William-Dorsch/3d-Printed-AAR-Control-Stand/AARcontroller(v6) - Release/air brake valves/automatic/auto Notch.stl

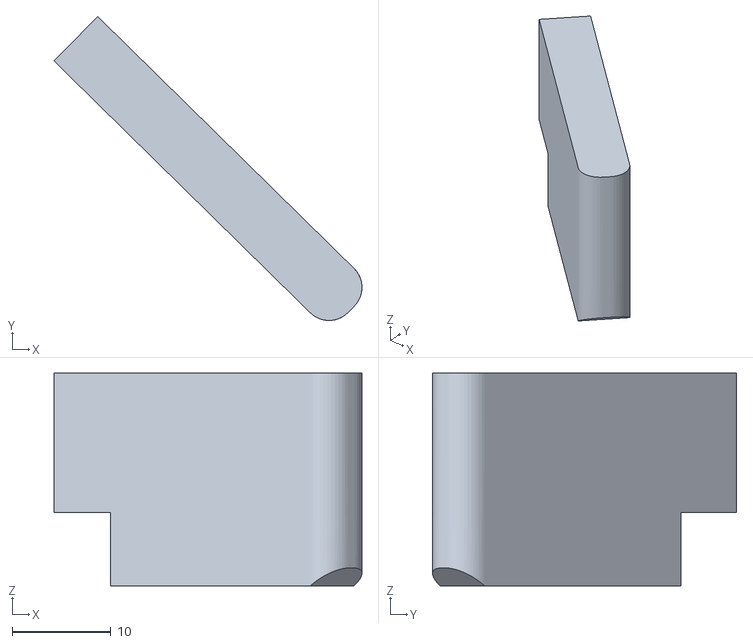
[picture p15: CAD file, 2026-03-23]
AARcontroller(v6) - Release/air brake valves/automatic/auto Notch.stl
31.1 x 30.7 x 21.5
