William-Dorsch/3d-Printed-AAR-Control-Stand/AARcontroller(v6) - Release/air brake valves/independent/indy housing.stl

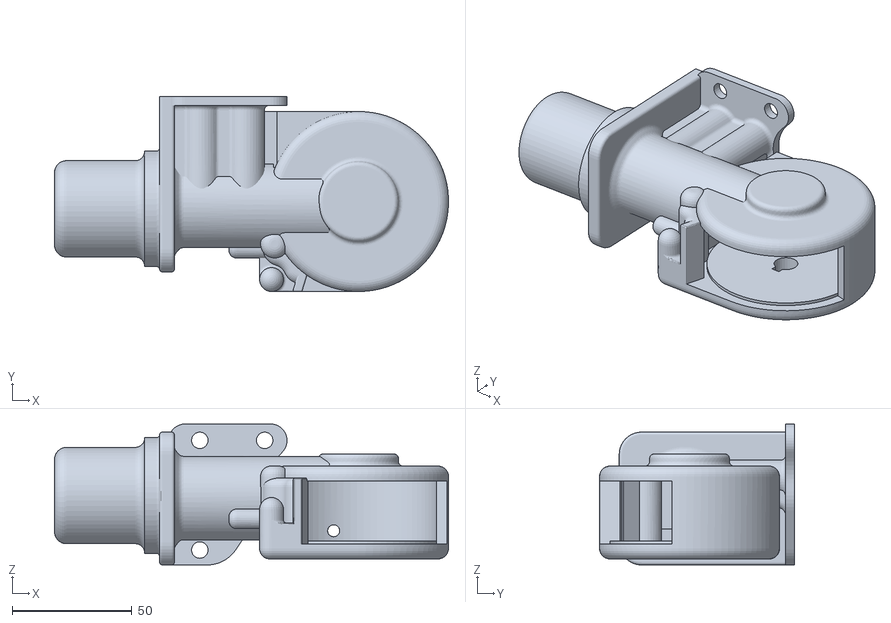
[picture p16: CAD file, 2025-12-22]
AARcontroller(v6) - Release/air brake valves/independent/indy housing.stl
164.2 x 81.3 x 58.8
