William-Dorsch/3d-Printed-AAR-Control-Stand/AARcontroller(v6) - Release/buttons and dials/breakers/linearSwitchBack.3mf

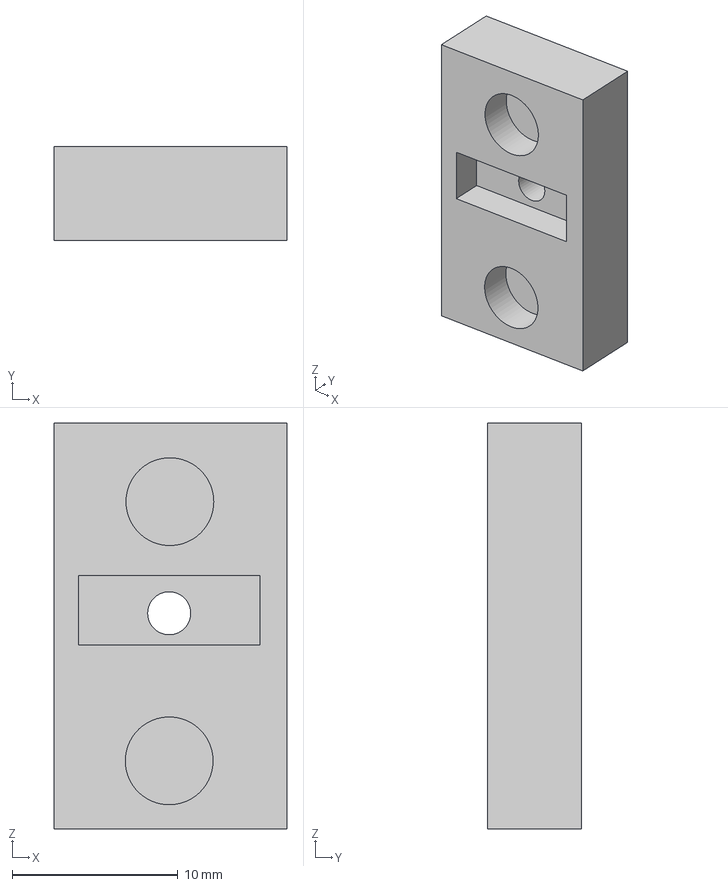
[picture p17: CAD file, 2025-12-27]
AARcontroller(v6) - Release/buttons and dials/breakers/linearSwitchBack.3mf
14.0 x 5.70 x 24.5 mm
