William-Dorsch/3d-Printed-AAR-Control-Stand/AARcontroller(v6) - Release/buttons and dials/horn/horn lever.3mf

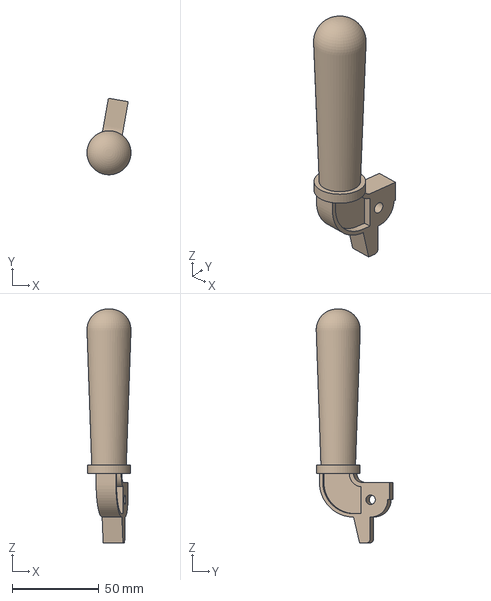
[picture p18: CAD file, 2026-02-25]
AARcontroller(v6) - Release/buttons and dials/horn/horn lever.3mf
25.4 x 44.2 x 135.0 mm
