William-Dorsch/3d-Printed-AAR-Control-Stand/AARcontroller(v6) - Release/buttons and dials/indicator light panel/indicatorLightHousing.stl

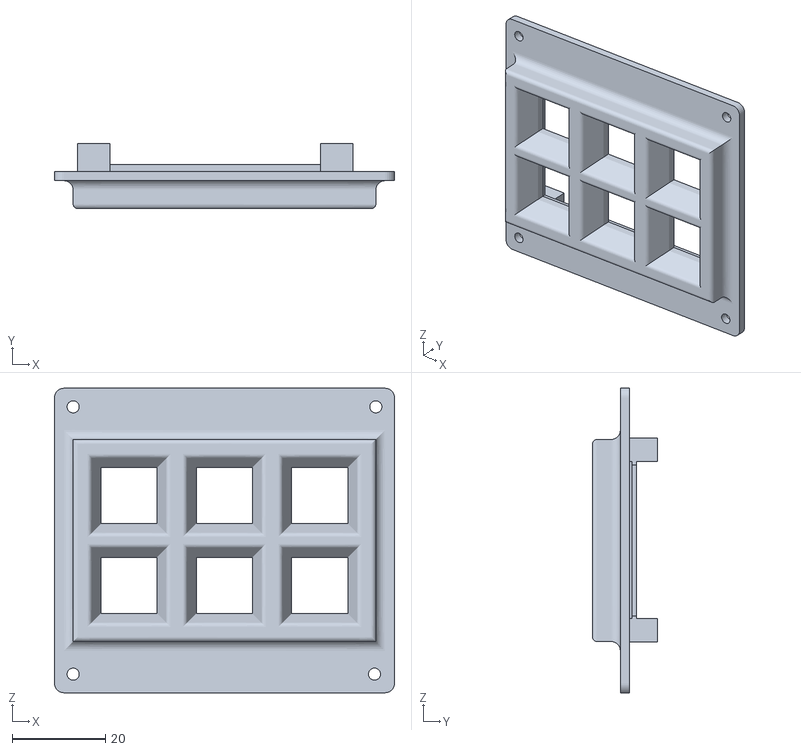
[picture p19: CAD file, 2025-12-22]
AARcontroller(v6) - Release/buttons and dials/indicator light panel/indicatorLightHousing.stl
72.9 x 14.0 x 65.3
