William-Dorsch/3d-Printed-AAR-Control-Stand/AARcontroller(v6) - Release/buttons and dials/light dials v2/rear light dial faceplate.3mf

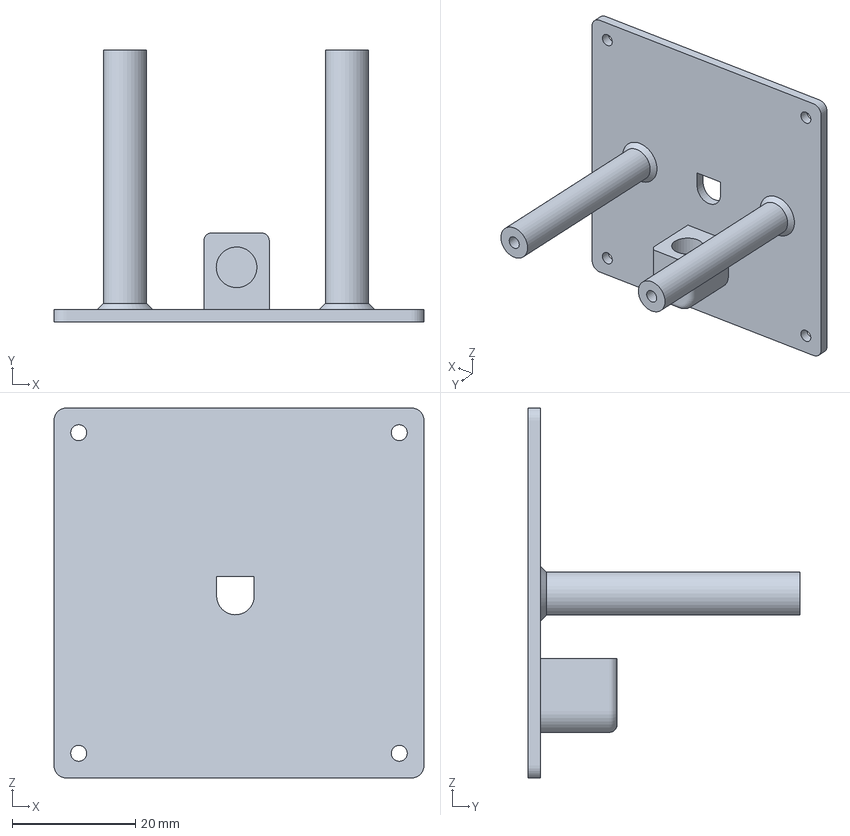
[picture p20: CAD file, 2026-03-18]
AARcontroller(v6) - Release/buttons and dials/light dials v2/rear light dial faceplate.3mf
60.0 x 44.1 x 60.0 mm
