William-Dorsch/3d-Printed-AAR-Control-Stand/AARcontroller(v6) - Release/cutout templates/light dial cutout.stl

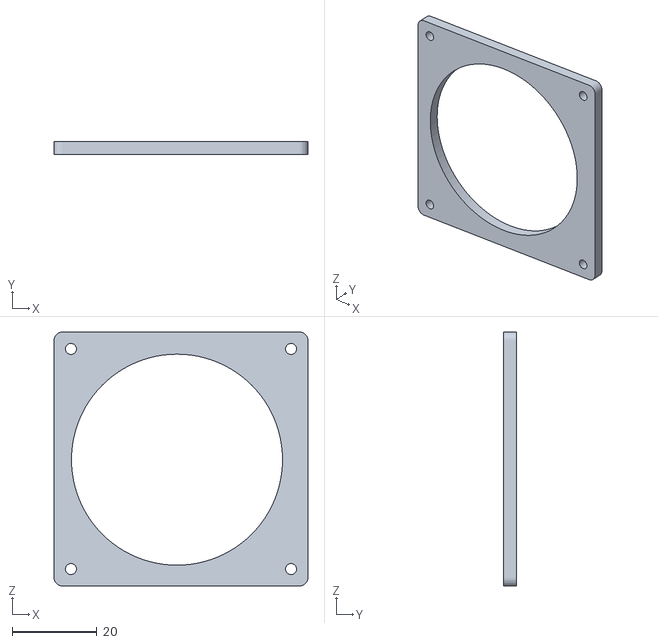
[picture p21: CAD file, 2025-12-22]
AARcontroller(v6) - Release/cutout templates/light dial cutout.stl
60.0 x 3.00 x 60.0
