William-Dorsch/3d-Printed-AAR-Control-Stand/AARcontroller(v6) - Release/throttle and dynamic brake/dynamic brake/dynamic brake label.stl

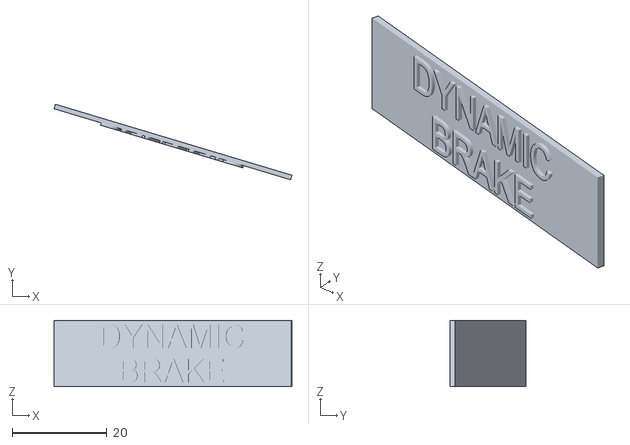
[picture p23: CAD file, 2025-12-22]
AARcontroller(v6) - Release/throttle and dynamic brake/dynamic brake/dynamic brake label.stl
50.3 x 16.0 x 14.0
