William-Dorsch/3d-Printed-AAR-Control-Stand/AARcontroller(v6) - Release/throttle and dynamic brake/throttle and db axle.stl

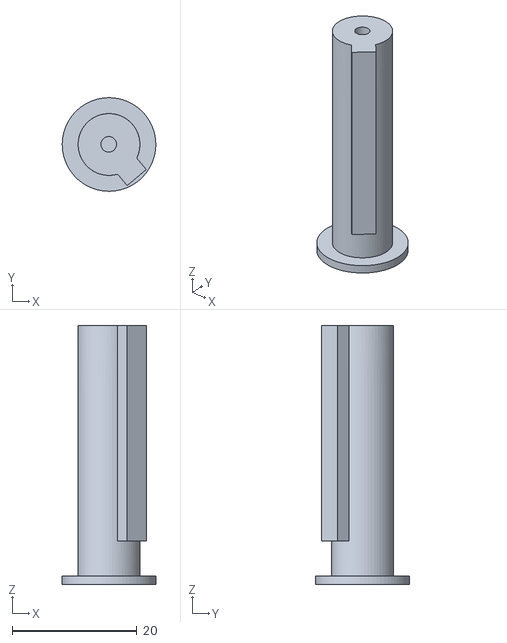
[picture p25: CAD file, 2025-12-22]
AARcontroller(v6) - Release/throttle and dynamic brake/throttle and db axle.stl
15.0 x 15.0 x 41.5
