William-Dorsch/3d-Printed-AAR-Control-Stand/AARcontroller(v6) - Release/throttle and dynamic brake/throttle/throttle notch v2.stl

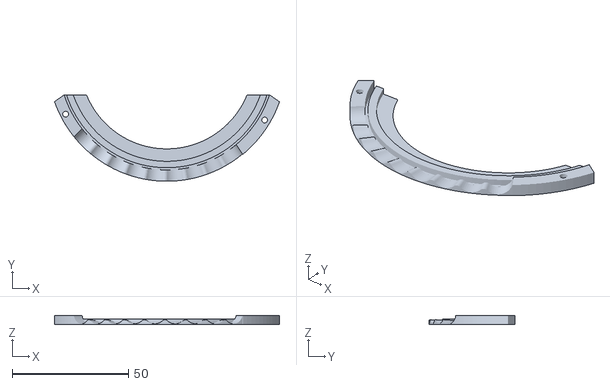
[picture p26: CAD file, 2025-12-22]
AARcontroller(v6) - Release/throttle and dynamic brake/throttle/throttle notch v2.stl
96.6 x 37.1 x 4.00
