William-Dorsch/3d-Printed-AAR-Control-Stand/AARcontroller(v6) - Release/air brake valves/automatic/26c upper housing (1).stl

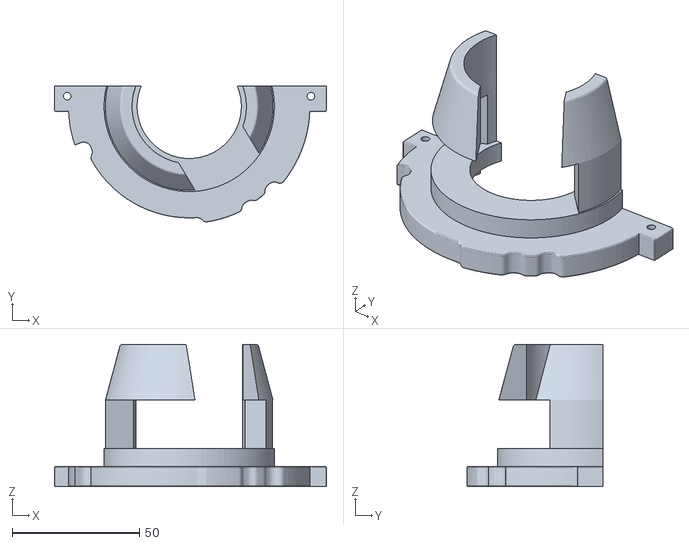
[picture p27: CAD file, 2025-12-22]
AARcontroller(v6) - Release/air brake valves/automatic/26c upper housing (1).stl
107.0 x 53.5 x 56.0
