William-Dorsch/3d-Printed-AAR-Control-Stand/AARcontroller(v6) - Release/air brake valves/independent/independentBailCap.stl

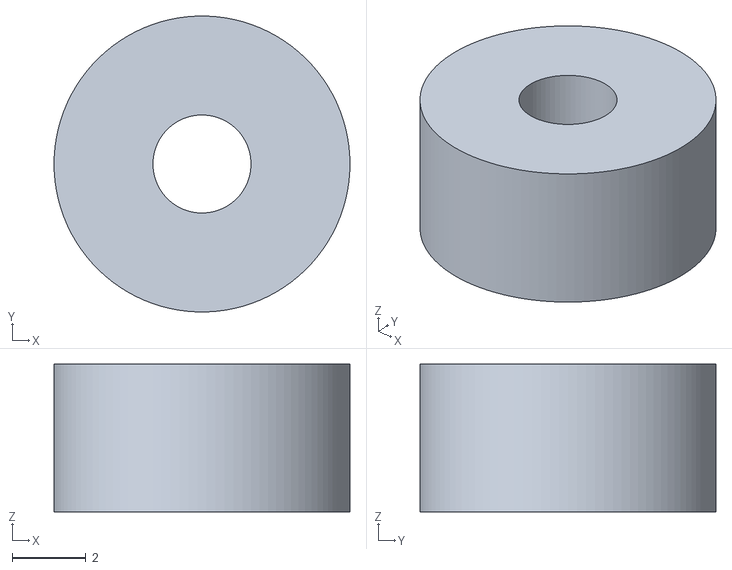
[picture p28: CAD file, 2025-12-22]
AARcontroller(v6) - Release/air brake valves/independent/independentBailCap.stl
8.00 x 8.00 x 4.00
