William-Dorsch/3d-Printed-AAR-Control-Stand/AARcontroller(v6) - Release/buttons and dials/breakers/linearSwitch.stl

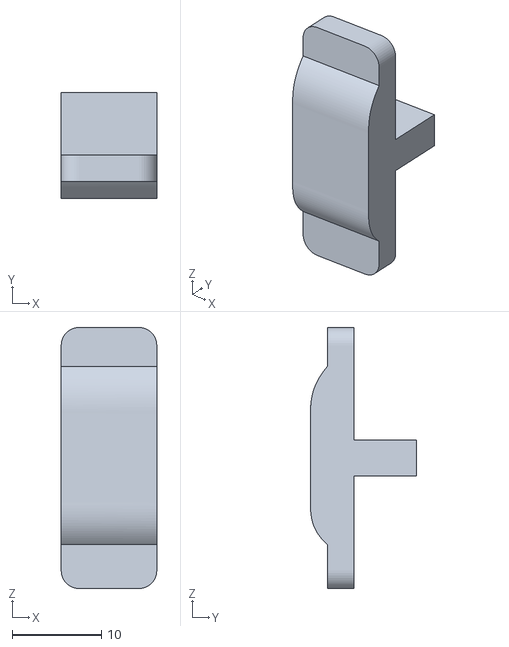
[picture p29: CAD file, 2025-12-22]
AARcontroller(v6) - Release/buttons and dials/breakers/linearSwitch.stl
10.7 x 11.9 x 29.3
