William-Dorsch/3d-Printed-AAR-Control-Stand/AARcontroller(v6) - Release/buttons and dials/buttons/button_test_base.stl

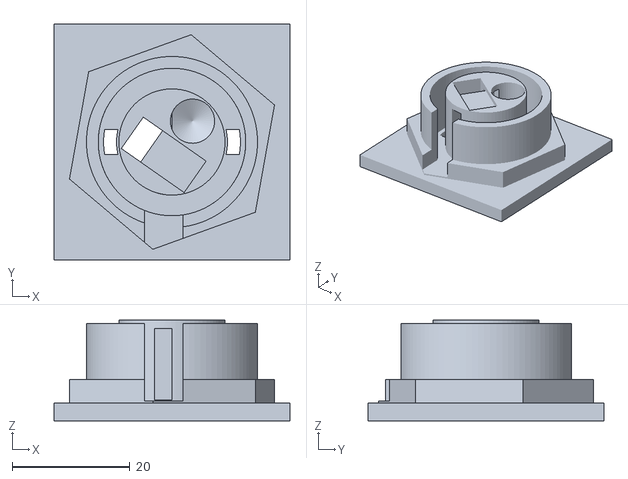
[picture p30: CAD file, 2025-12-22]
AARcontroller(v6) - Release/buttons and dials/buttons/button_test_base.stl
40.0 x 40.0 x 17.1
