William-Dorsch/3d-Printed-AAR-Control-Stand/AARcontroller(v6) - Release/buttons and dials/horn/horn lever base.3mf

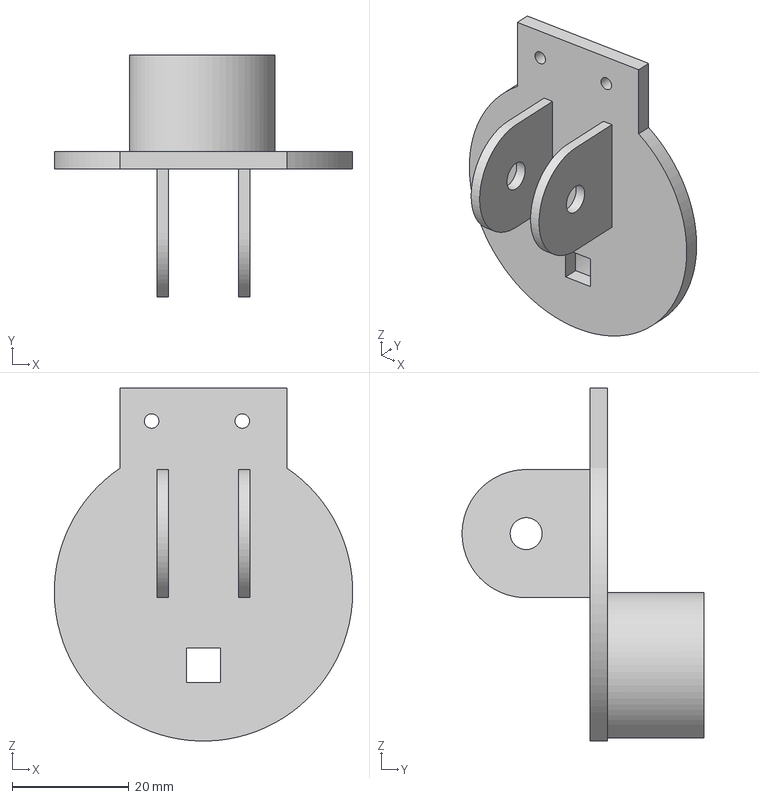
[picture p31: CAD file, 2026-02-25]
AARcontroller(v6) - Release/buttons and dials/horn/horn lever base.3mf
51.2 x 41.5 x 60.6 mm
