William-Dorsch/3d-Printed-AAR-Control-Stand/AARcontroller(v6) - Release/cutout templates/automatic cutout.stl

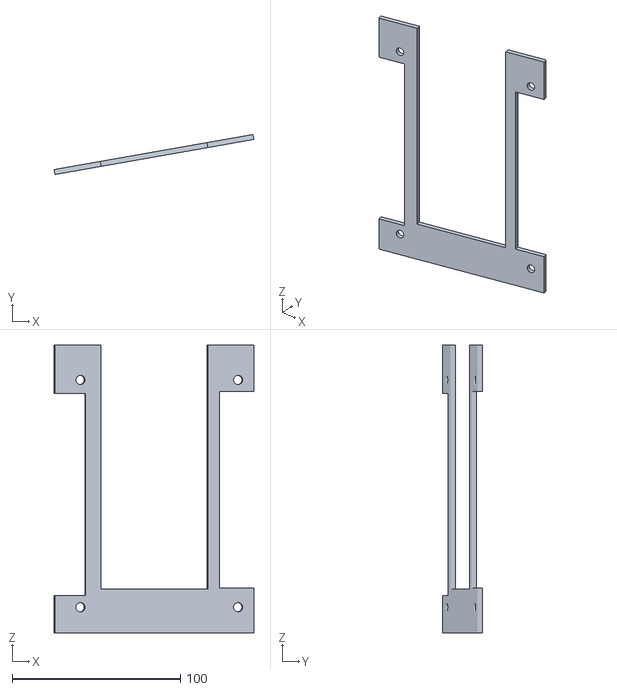
[picture p32: CAD file, 2025-12-22]
AARcontroller(v6) - Release/cutout templates/automatic cutout.stl
118.7 x 23.8 x 171.0
