William-Dorsch/3d-Printed-AAR-Control-Stand/AARcontroller(v6) - Release/reverser/reverser_subframe v2.3mf

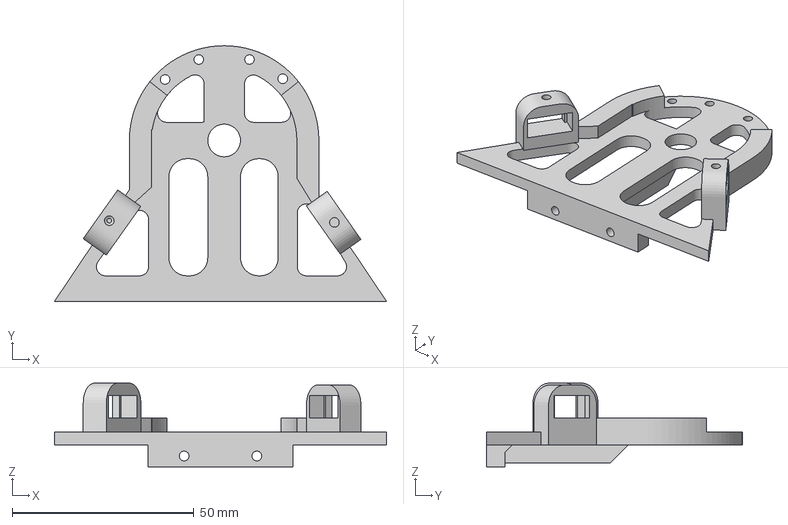
[picture p33: CAD file, 2026-02-25]
AARcontroller(v6) - Release/reverser/reverser_subframe v2.3mf
91.3 x 70.3 x 23.1 mm
