William-Dorsch/3d-Printed-AAR-Control-Stand/AARcontroller(v6) - Release/throttle and dynamic brake/dynamic brake/dynamic cover.stl

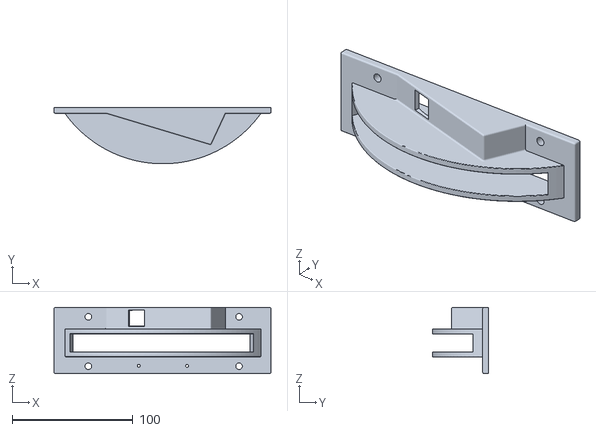
[picture p34: CAD file, 2025-12-22]
AARcontroller(v6) - Release/throttle and dynamic brake/dynamic brake/dynamic cover.stl
180.0 x 46.8 x 55.0
