William-Dorsch/3d-Printed-AAR-Control-Stand/AARcontroller(v6) - Release/throttle and dynamic brake/notch indicators/3.stl

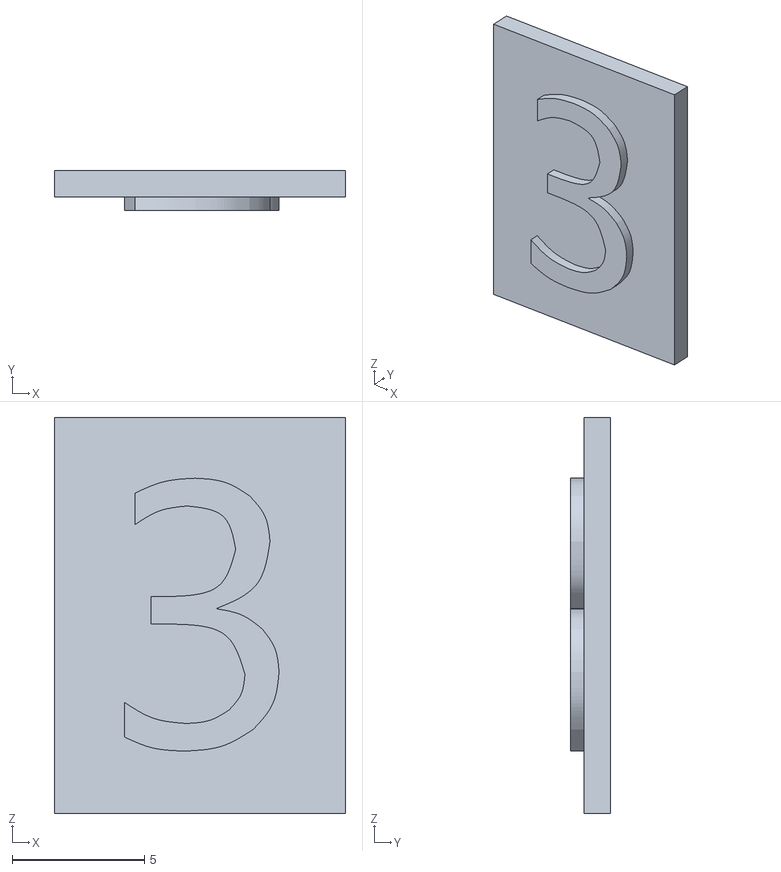
[picture p35: CAD file, 2025-12-22]
AARcontroller(v6) - Release/throttle and dynamic brake/notch indicators/3.stl
11.0 x 1.50 x 15.0
