William-Dorsch/3d-Printed-AAR-Control-Stand/AARcontroller(v6) - Release/air brake valves/automatic/auto brake handle.stl

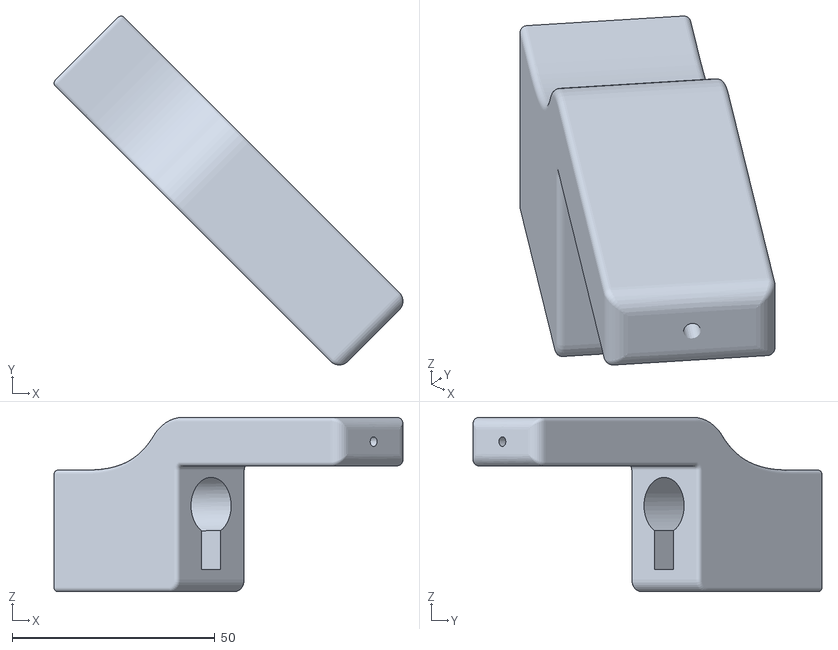
[picture p36: CAD file, 2025-12-22]
AARcontroller(v6) - Release/air brake valves/automatic/auto brake handle.stl
86.0 x 86.0 x 43.0
