William-Dorsch/3d-Printed-AAR-Control-Stand/AARcontroller(v6) - Release/air brake valves/independent/indy potentiometer housing.stl

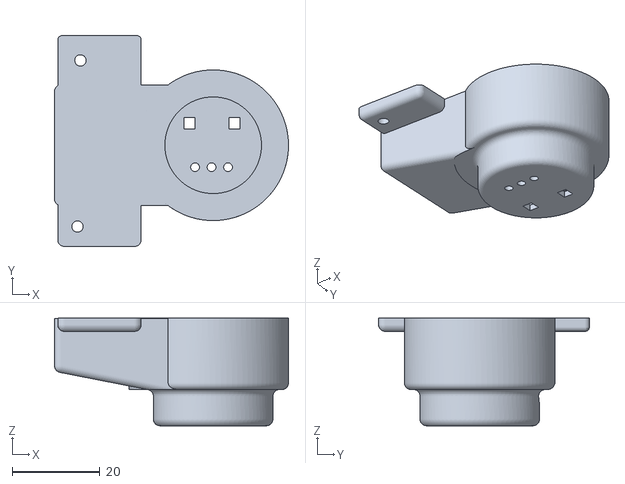
[picture p37: CAD file, 2025-12-22]
AARcontroller(v6) - Release/air brake valves/independent/indy potentiometer housing.stl
53.3 x 48.0 x 24.5
