William-Dorsch/3d-Printed-AAR-Control-Stand/AARcontroller(v6) - Release/buttons and dials/buttons/buttonCap.stl

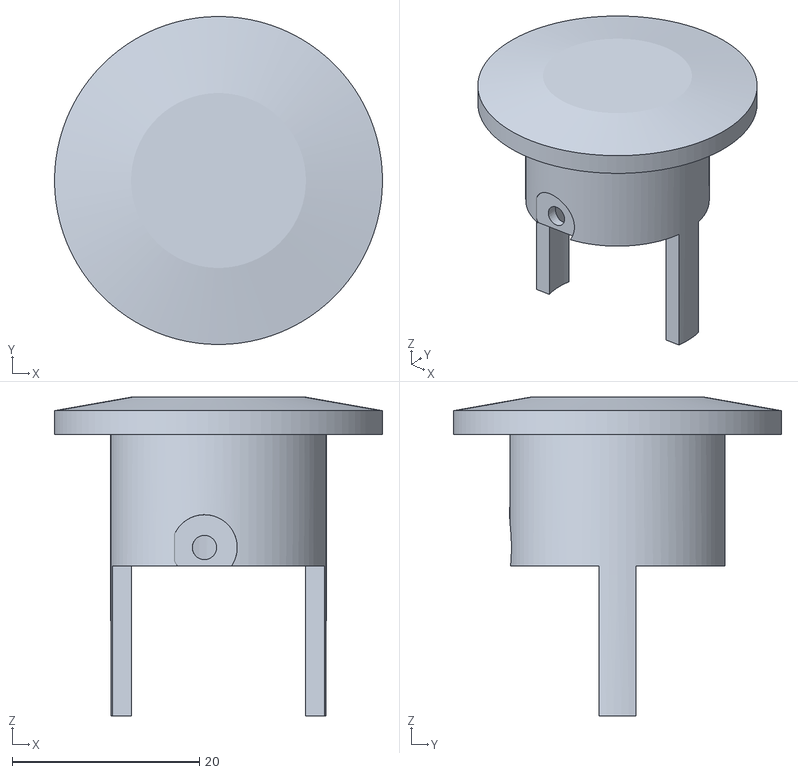
[picture p38: CAD file, 2025-12-22]
AARcontroller(v6) - Release/buttons and dials/buttons/buttonCap.stl
35.0 x 35.0 x 34.0
