William-Dorsch/3d-Printed-AAR-Control-Stand/AARcontroller(v6) - Release/buttons and dials/horn/switch mount.3mf

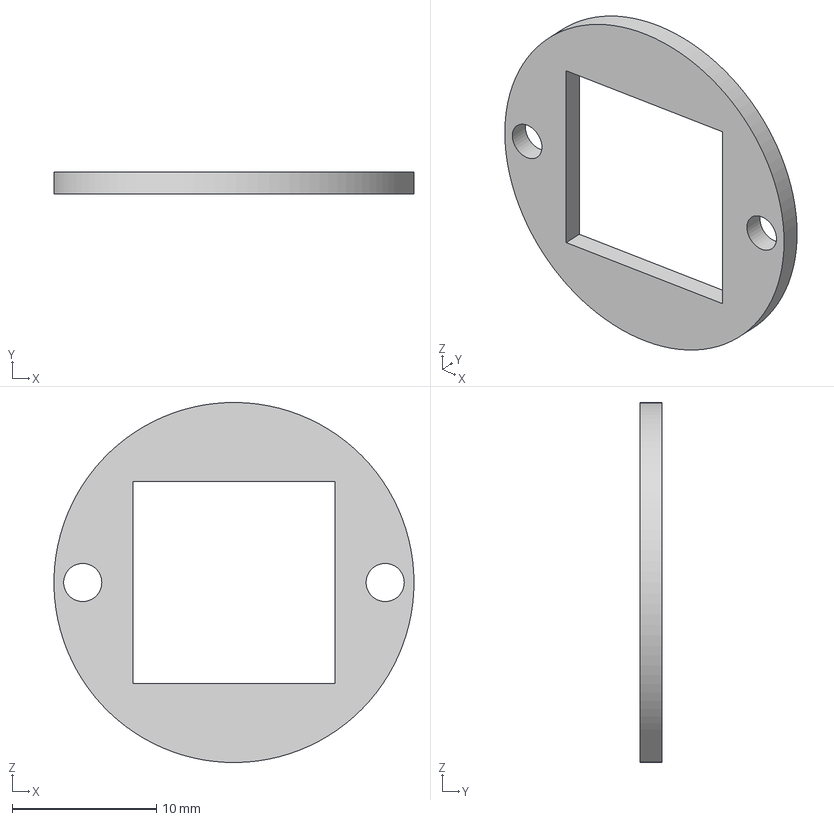
[picture p39: CAD file, 2026-02-25]
AARcontroller(v6) - Release/buttons and dials/horn/switch mount.3mf
25.0 x 1.50 x 25.0 mm
