William-Dorsch/3d-Printed-AAR-Control-Stand/AARcontroller(v6) - Release/buttons and dials/light dials v2/light dial housing.3mf

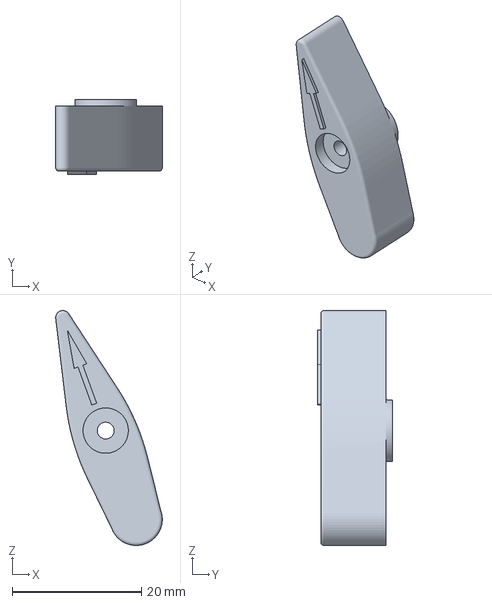
[picture p40: CAD file, 2026-02-25]
AARcontroller(v6) - Release/buttons and dials/light dials v2/light dial housing.3mf
16.5 x 11.5 x 36.3 mm
