William-Dorsch/3d-Printed-AAR-Control-Stand/AARcontroller(v6) - Release/cutout templates/horn cutout.stl

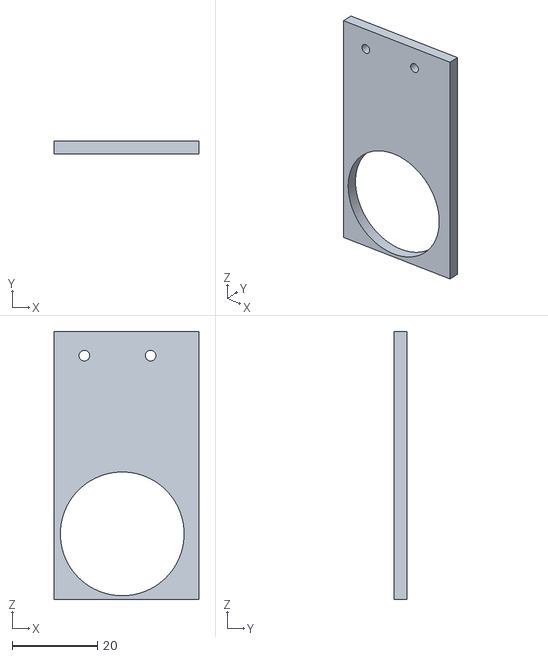
[picture p41: CAD file, 2025-12-22]
AARcontroller(v6) - Release/cutout templates/horn cutout.stl
34.0 x 3.00 x 63.0
