William-Dorsch/3d-Printed-AAR-Control-Stand/AARcontroller(v6) - Release/reverser/reverser_carrier.3mf

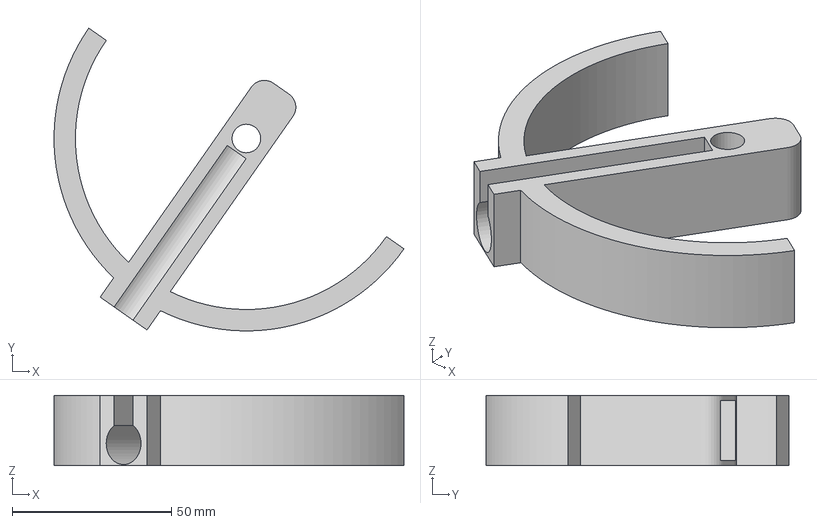
[picture p42: CAD file, 2026-02-25]
AARcontroller(v6) - Release/reverser/reverser_carrier.3mf
110.1 x 95.2 x 22.1 mm
