William-Dorsch/3d-Printed-AAR-Control-Stand/AARcontroller(v6) - Release/spring object.stl

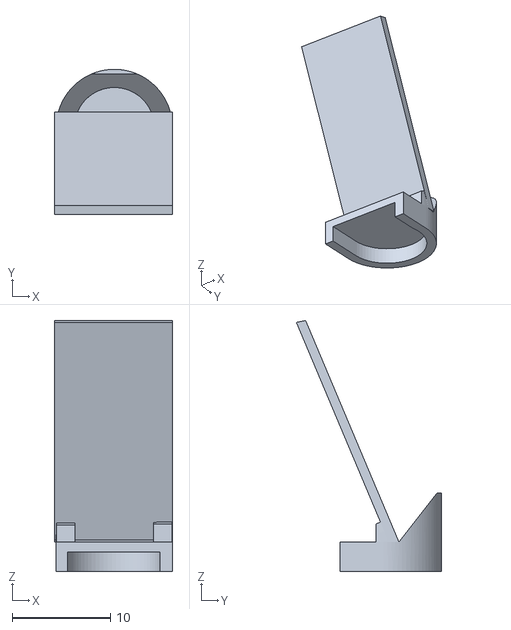
[picture p43: CAD file, 2025-12-22]
AARcontroller(v6) - Release/spring object.stl
12.0 x 14.8 x 25.5
