William-Dorsch/3d-Printed-AAR-Control-Stand/AARcontroller(v6) - Release/throttle and dynamic brake/dynamic brake/dynamic notch indicator holder.stl

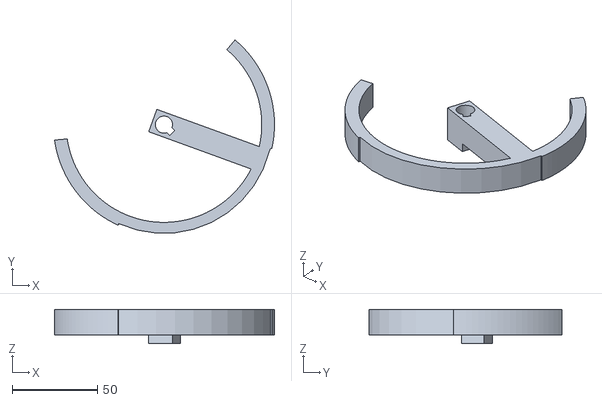
[picture p44: CAD file, 2025-12-22]
AARcontroller(v6) - Release/throttle and dynamic brake/dynamic brake/dynamic notch indicator holder.stl
129.4 x 113.6 x 20.0
