William-Dorsch/3d-Printed-AAR-Control-Stand/AARcontroller(v6) - Release/air brake valves/automatic/auto brake carrier.stl

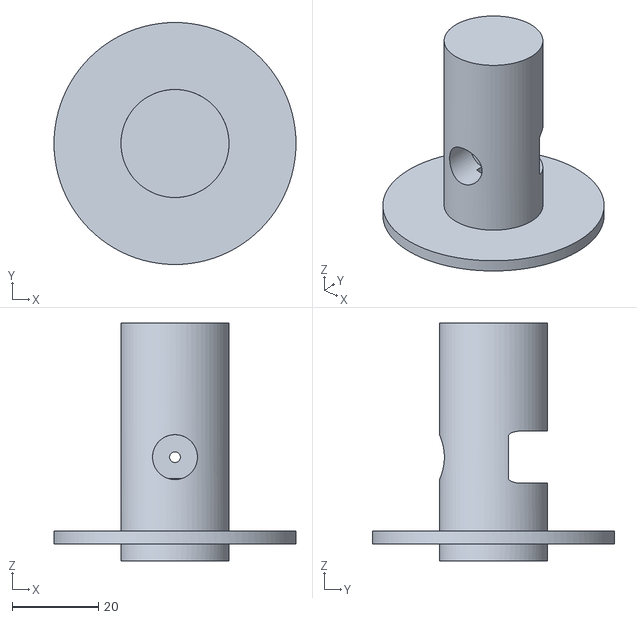
[picture p45: CAD file, 2025-12-22]
AARcontroller(v6) - Release/air brake valves/automatic/auto brake carrier.stl
56.0 x 56.0 x 55.0
