William-Dorsch/3d-Printed-AAR-Control-Stand/AARcontroller(v6) - Release/air brake valves/independent/independetBailShaft.stl

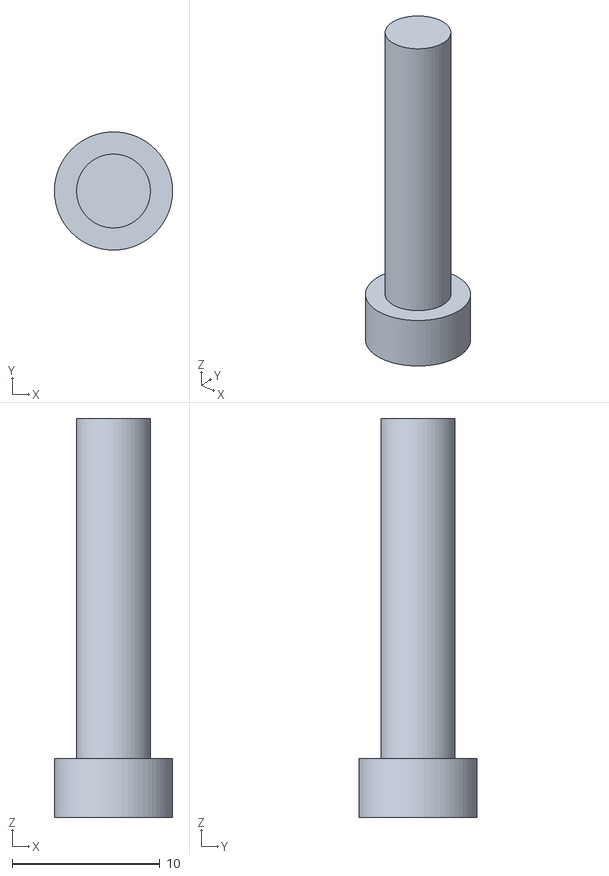
[picture p46: CAD file, 2025-12-22]
AARcontroller(v6) - Release/air brake valves/independent/independetBailShaft.stl
8.00 x 7.99 x 27.0
