William-Dorsch/3d-Printed-AAR-Control-Stand/AARcontroller(v6) - Release/buttons and dials/light dials v2/light dial innter housing.3mf

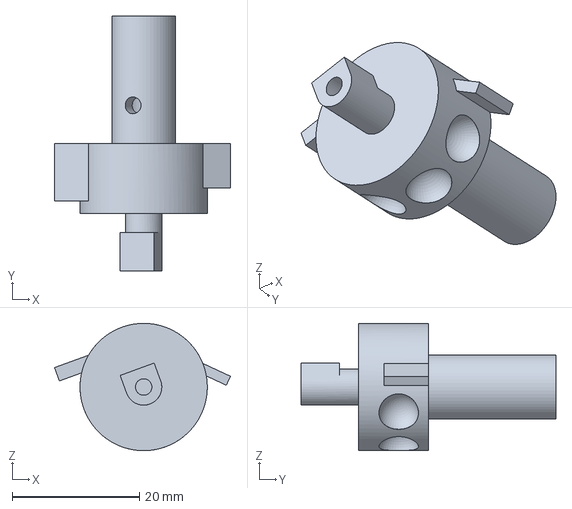
[picture p47: CAD file, 2026-02-25]
AARcontroller(v6) - Release/buttons and dials/light dials v2/light dial innter housing.3mf
27.6 x 40.0 x 20.0 mm
