William-Dorsch/3d-Printed-AAR-Control-Stand/AARcontroller(v6) - Release/cutout templates/reverser cutout.stl

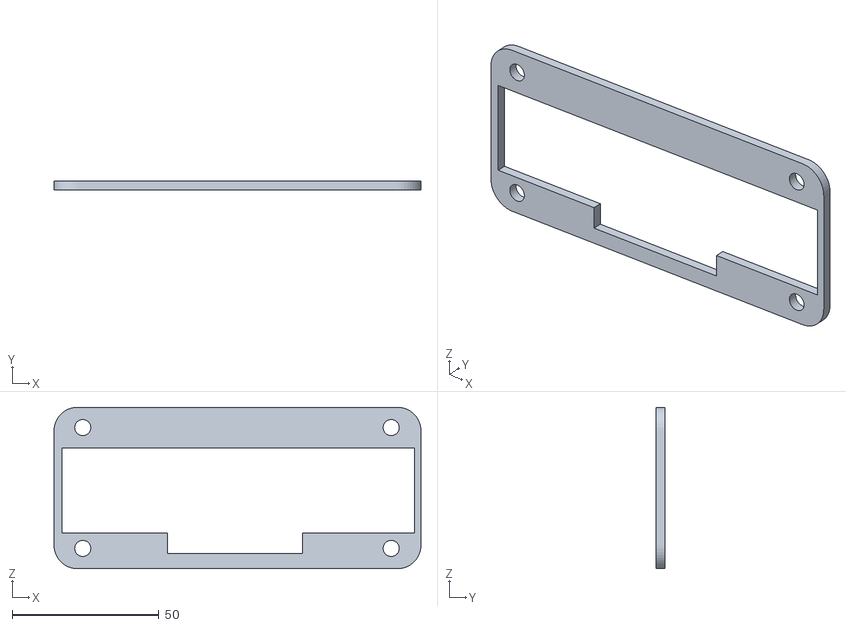
[picture p48: CAD file, 2025-12-22]
AARcontroller(v6) - Release/cutout templates/reverser cutout.stl
125.0 x 3.00 x 55.0
