William-Dorsch/3d-Printed-AAR-Control-Stand/AARcontroller(v6) - Release/horn v4.stl

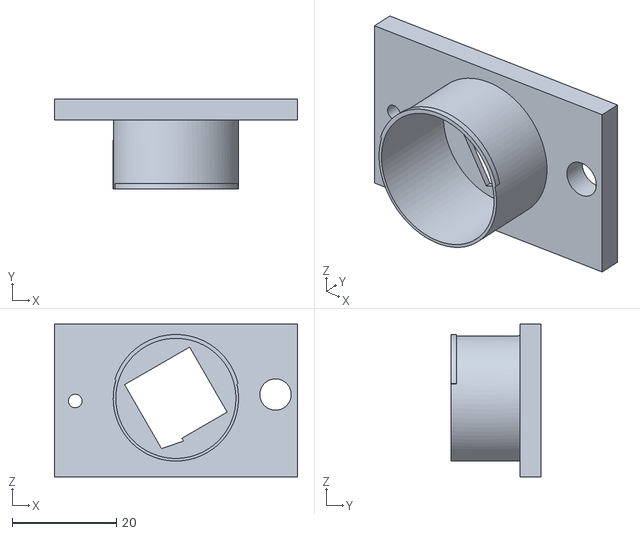
[picture p49: CAD file, 2025-12-22]
AARcontroller(v6) - Release/horn v4.stl
46.5 x 17.2 x 29.3
