William-Dorsch/3d-Printed-AAR-Control-Stand/AARcontroller(v6) - Release/reverser/reverser notch plate.3mf

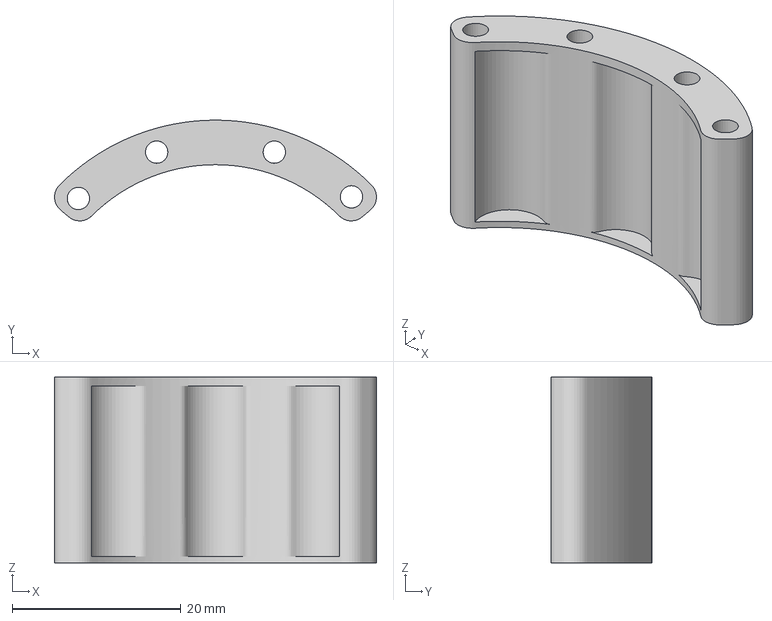
[picture p50: CAD file, 2026-02-25]
AARcontroller(v6) - Release/reverser/reverser notch plate.3mf
38.2 x 11.9 x 22.0 mm
