William-Dorsch/3d-Printed-AAR-Control-Stand/AARcontroller(v6) - Release/throttle and dynamic brake/dynamic brake/dynamic notch plunger.stl

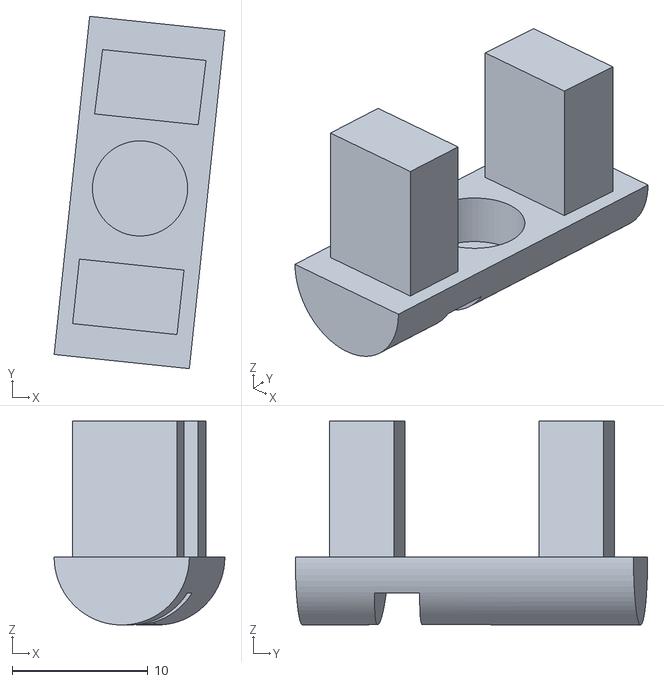
[picture p51: CAD file, 2025-12-22]
AARcontroller(v6) - Release/throttle and dynamic brake/dynamic brake/dynamic notch plunger.stl
12.6 x 25.9 x 15.0
