William-Dorsch/3d-Printed-AAR-Control-Stand/AARcontroller(v6) - Release/throttle and dynamic brake/throttle/throttle notch indicator holder.stl

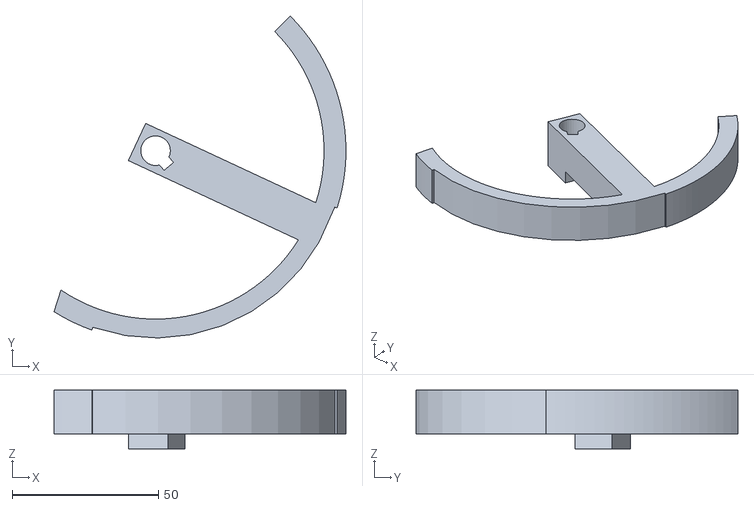
[picture p52: CAD file, 2025-12-22]
AARcontroller(v6) - Release/throttle and dynamic brake/throttle/throttle notch indicator holder.stl
99.7 x 109.9 x 20.0
