William-Dorsch/3d-Printed-AAR-Control-Stand/AARcontroller(v6) - Release/air brake valves/automatic/auto brake grip.stl

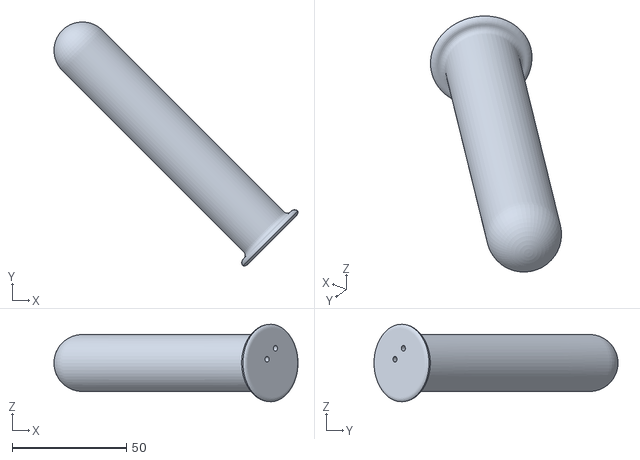
[picture p53: CAD file, 2025-12-22]
AARcontroller(v6) - Release/air brake valves/automatic/auto brake grip.stl
106.9 x 106.9 x 34.0
