William-Dorsch/3d-Printed-AAR-Control-Stand/AARcontroller(v6) - Release/air brake valves/independent/indy axle.stl

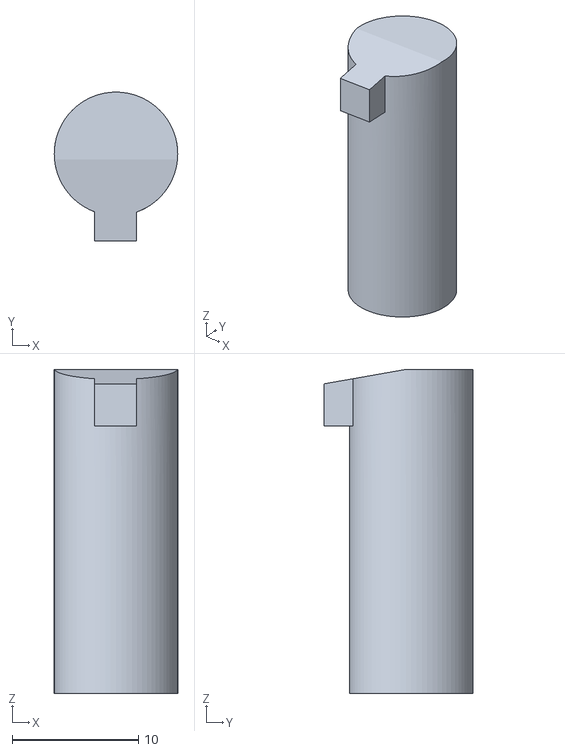
[picture p54: CAD file, 2025-12-22]
AARcontroller(v6) - Release/air brake valves/independent/indy axle.stl
9.80 x 11.8 x 25.7
