William-Dorsch/3d-Printed-AAR-Control-Stand/AARcontroller(v6) - Release/buttons and dials/light dials v2/light dial potentiometer holder (1) (1).3mf

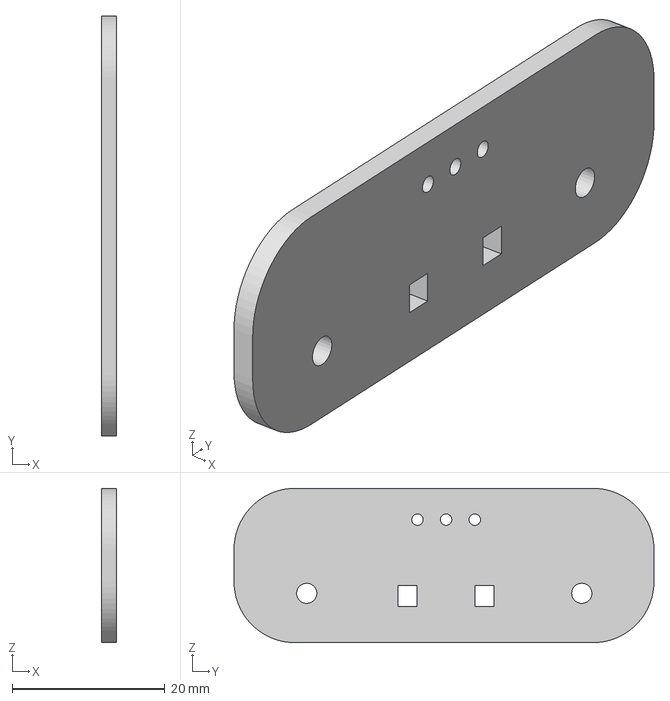
[picture p55: CAD file, 2026-02-25]
AARcontroller(v6) - Release/buttons and dials/light dials v2/light dial potentiometer holder (1) (1).3mf
2.00 x 55.0 x 20.2 mm
