William-Dorsch/3d-Printed-AAR-Control-Stand/AARcontroller(v6) - Release/cutout templates/linear switch cutout.stl

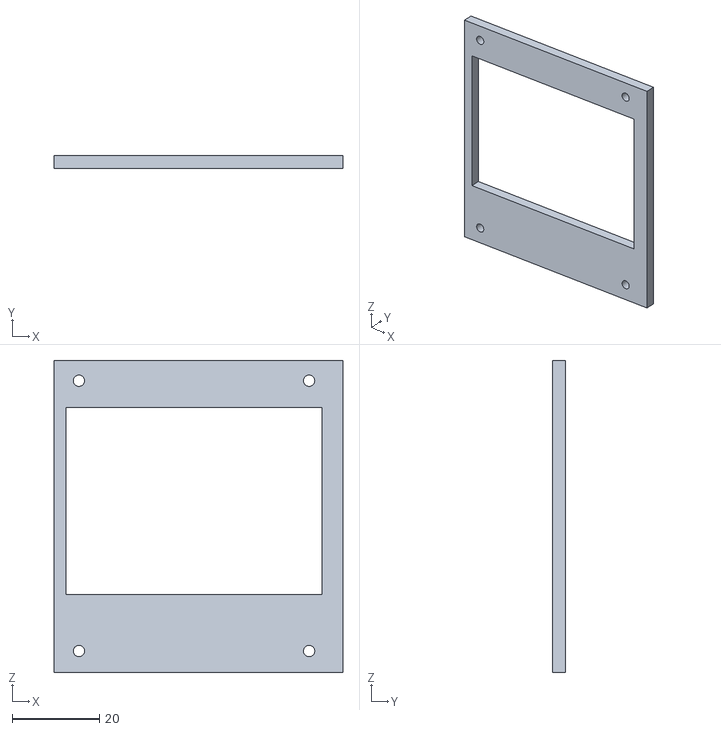
[picture p56: CAD file, 2025-12-22]
AARcontroller(v6) - Release/cutout templates/linear switch cutout.stl
66.2 x 3.00 x 71.5
