William-Dorsch/3d-Printed-AAR-Control-Stand/AARcontroller(v6) - Release/reverser/reverser axle v3.3mf

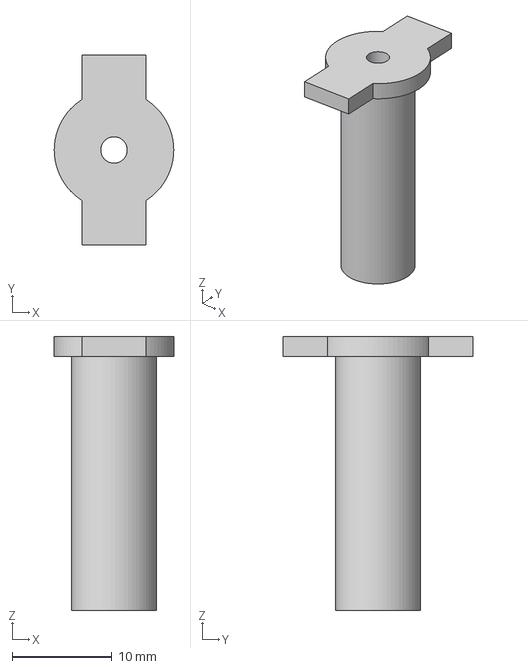
[picture p57: CAD file, 2026-02-25]
AARcontroller(v6) - Release/reverser/reverser axle v3.3mf
12.0 x 19.1 x 27.5 mm
