William-Dorsch/3d-Printed-AAR-Control-Stand/AARcontroller(v6) - Release/spring object2.stl

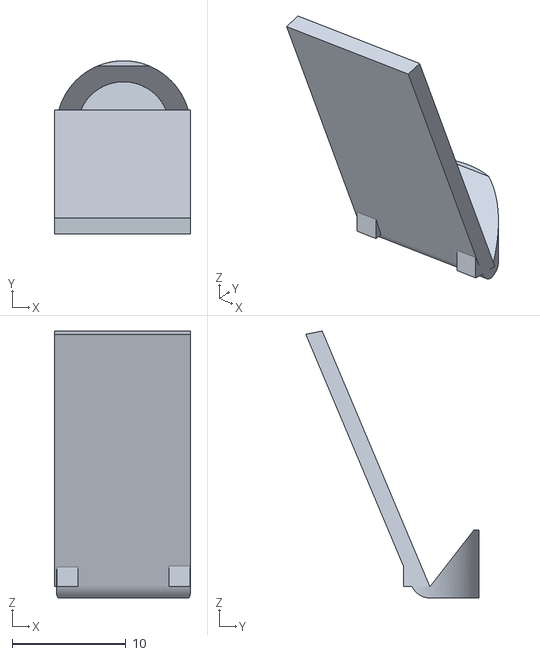
[picture p58: CAD file, 2025-12-22]
AARcontroller(v6) - Release/spring object2.stl
12.0 x 15.3 x 23.5
