William-Dorsch/3d-Printed-AAR-Control-Stand/AARcontroller(v6) - Release/throttle and dynamic brake/dynamic brake/dynamic notches.stl

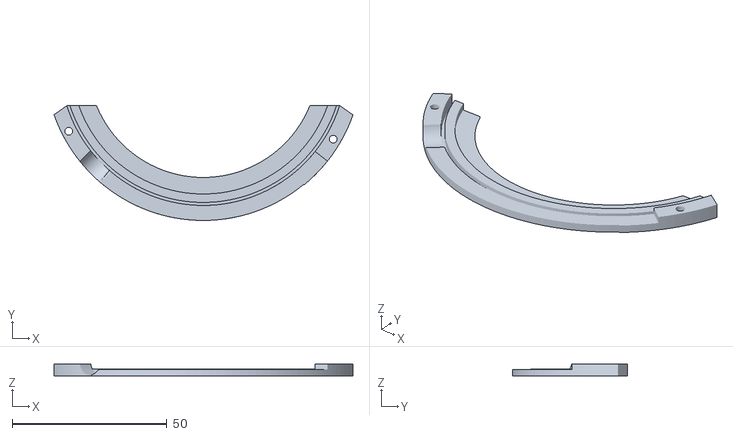
[picture p59: CAD file, 2025-12-22]
AARcontroller(v6) - Release/throttle and dynamic brake/dynamic brake/dynamic notches.stl
96.6 x 37.1 x 4.00
