William-Dorsch/3d-Printed-AAR-Control-Stand/AARcontroller(v6) - Release/throttle and dynamic brake/throttle/power throttle label.stl

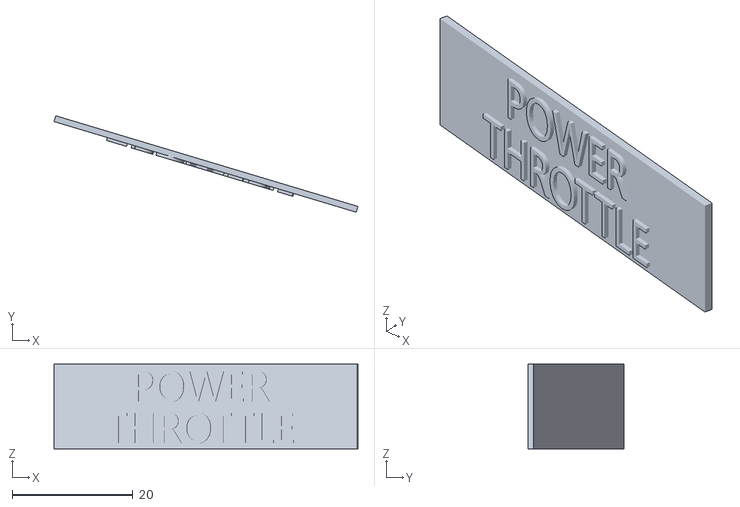
[picture p60: CAD file, 2025-12-22]
AARcontroller(v6) - Release/throttle and dynamic brake/throttle/power throttle label.stl
50.3 x 16.0 x 14.0
