William-Dorsch/3d-Printed-AAR-Control-Stand/AARcontroller(v6) - Release/air brake valves/automatic/26c lower housing (1) (1) (1).stl

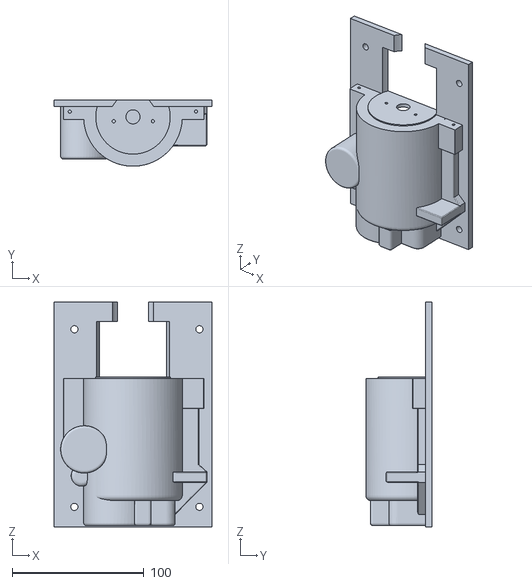
[picture p61: CAD file, 2025-12-22]
AARcontroller(v6) - Release/air brake valves/automatic/26c lower housing (1) (1) (1).stl
120.0 x 50.5 x 171.0
