William-Dorsch/3d-Printed-AAR-Control-Stand/AARcontroller(v6) - Release/air brake valves/independent/indy micrswitch handle.stl

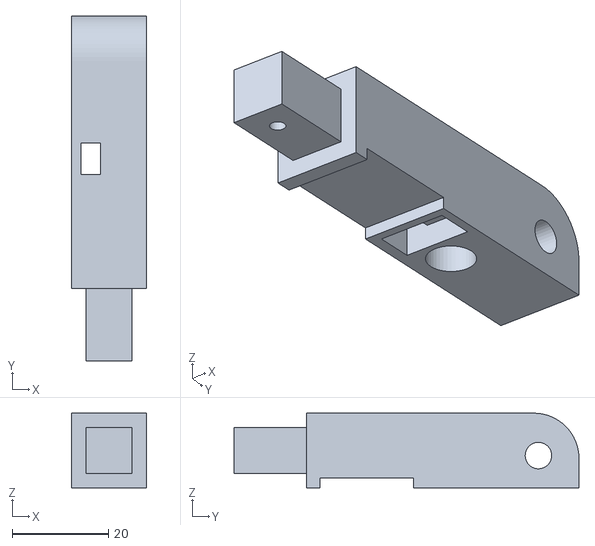
[picture p62: CAD file, 2025-12-22]
AARcontroller(v6) - Release/air brake valves/independent/indy micrswitch handle.stl
15.5 x 71.6 x 15.5
