William-Dorsch/3d-Printed-AAR-Control-Stand/AARcontroller(v6) - Release/cutout templates/independent cutout'.stl

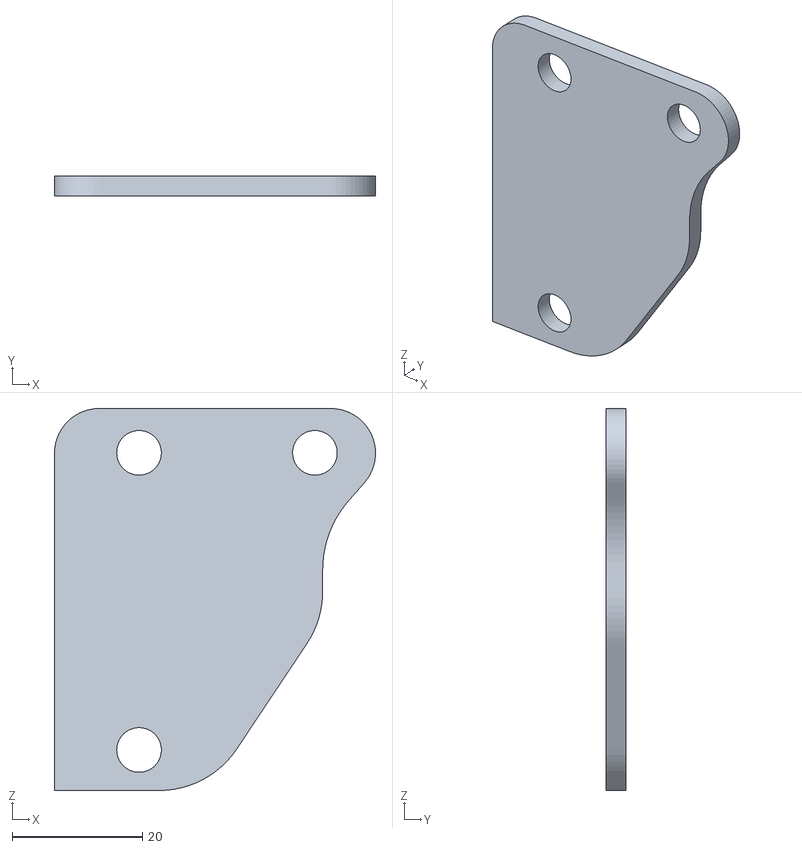
[picture p63: CAD file, 2025-12-22]
AARcontroller(v6) - Release/cutout templates/independent cutout'.stl
49.4 x 3.00 x 58.8
