William-Dorsch/3d-Printed-AAR-Control-Stand/AARcontroller(v6) - Release/light dial housing (1).stl

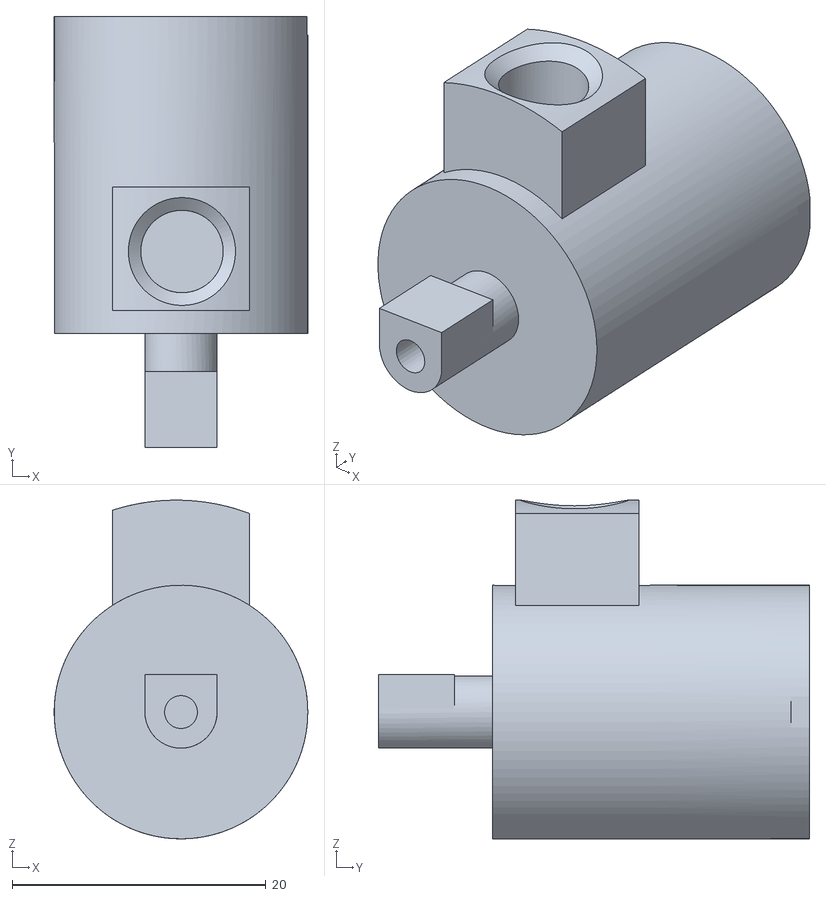
[picture p64: CAD file, 2025-12-22]
AARcontroller(v6) - Release/light dial housing (1).stl
20.0 x 34.0 x 26.7
