William-Dorsch/3d-Printed-AAR-Control-Stand/AARcontroller(v6) - Release/reverser/reverser cover.stl

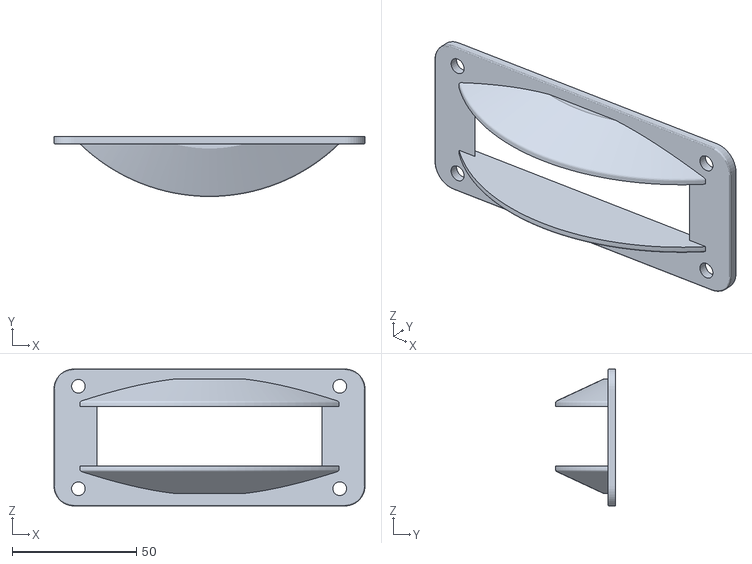
[picture p65: CAD file, 2025-12-22]
AARcontroller(v6) - Release/reverser/reverser cover.stl
125.0 x 24.1 x 55.0
