William-Dorsch/3d-Printed-AAR-Control-Stand/AARcontroller(v6) - Release/AAR _ F40 stand (v6) v22.stl

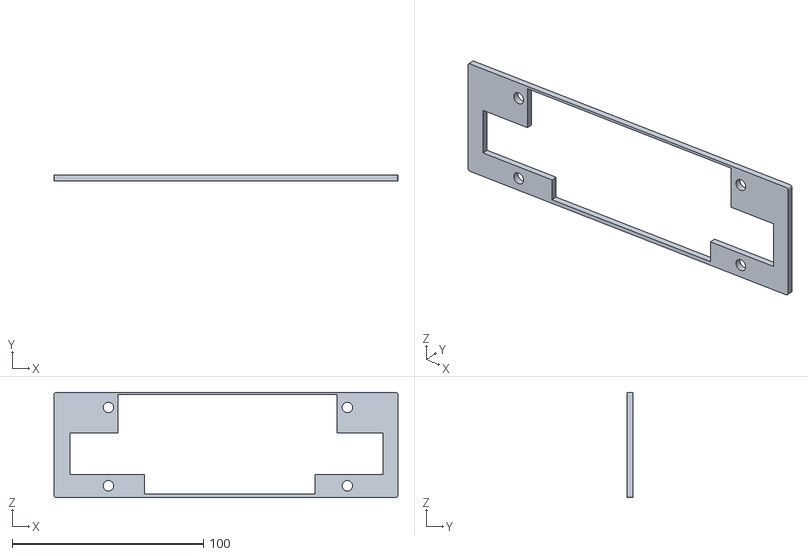
[picture p67: CAD file, 2025-12-22]
AARcontroller(v6) - Release/AAR _ F40 stand (v6) v22.stl
180.0 x 3.00 x 55.0
