William-Dorsch/3d-Printed-AAR-Control-Stand/AARcontroller(v6) - Release/air brake valves/automatic/auto brake axlew.stl

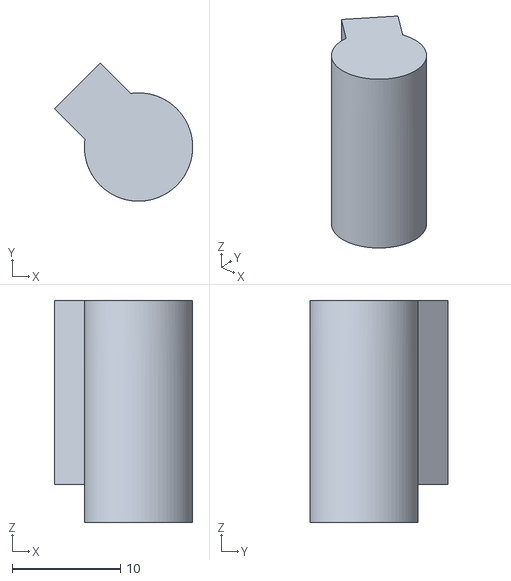
[picture p68: CAD file, 2025-12-22]
AARcontroller(v6) - Release/air brake valves/automatic/auto brake axlew.stl
12.8 x 12.8 x 20.5
