William-Dorsch/3d-Printed-AAR-Control-Stand/AARcontroller(v6) - Release/air brake valves/independent/indy inner housing.stl

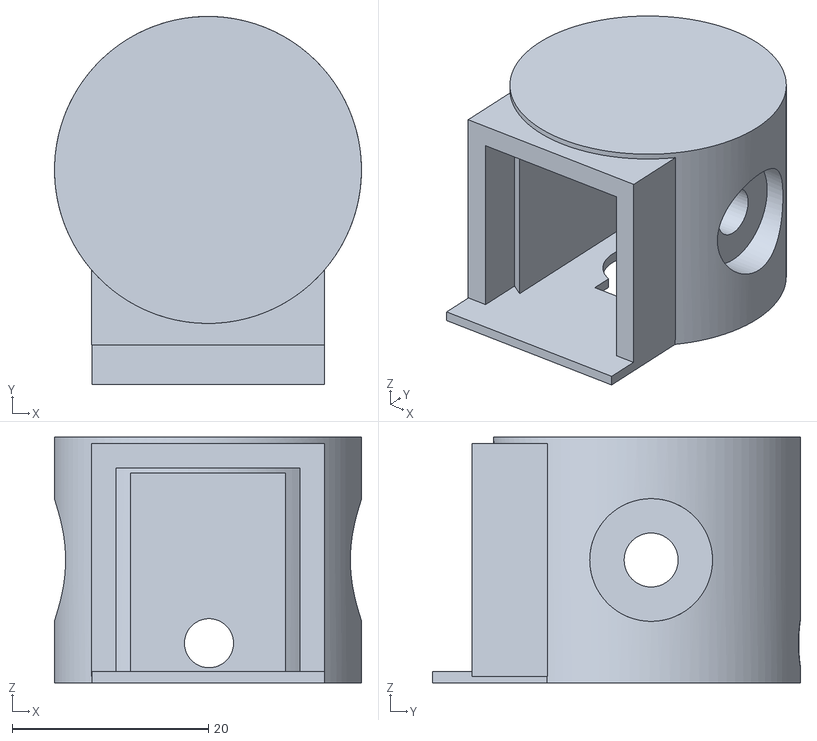
[picture p69: CAD file, 2025-12-22]
AARcontroller(v6) - Release/air brake valves/independent/indy inner housing.stl
31.2 x 37.5 x 25.0
