William-Dorsch/3d-Printed-AAR-Control-Stand/AARcontroller(v6) - Release/cutout templates/push button cutout.stl

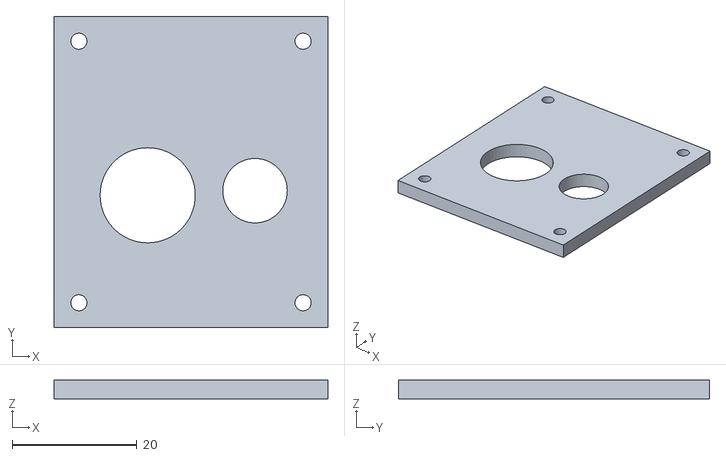
[picture p70: CAD file, 2025-12-22]
AARcontroller(v6) - Release/cutout templates/push button cutout.stl
44.0 x 50.0 x 3.00
