William-Dorsch/3d-Printed-AAR-Control-Stand/AARcontroller(v6) - Release/throttle handle (1) (1).stl

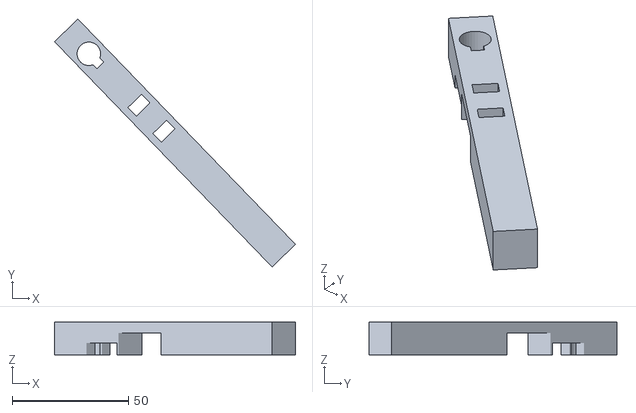
[picture p72: CAD file, 2025-12-22]
AARcontroller(v6) - Release/throttle handle (1) (1).stl
103.6 x 106.6 x 14.0
