William-Dorsch/3d-Printed-AAR-Control-Stand/AARcontroller(v6) - Release/throttle handle.stl

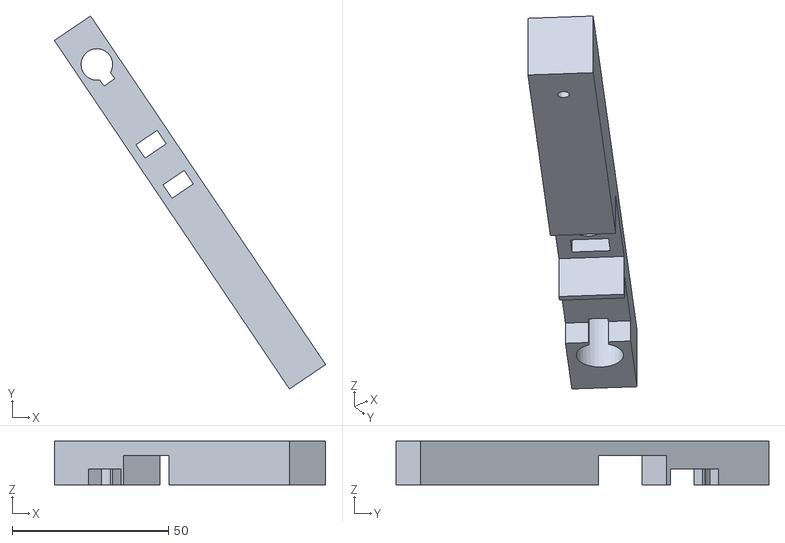
[picture p73: CAD file, 2025-12-22]
AARcontroller(v6) - Release/throttle handle.stl
86.9 x 119.5 x 14.0
