William-Dorsch/3d-Printed-AAR-Control-Stand/AARcontroller(v6) - Release/Body669.stl

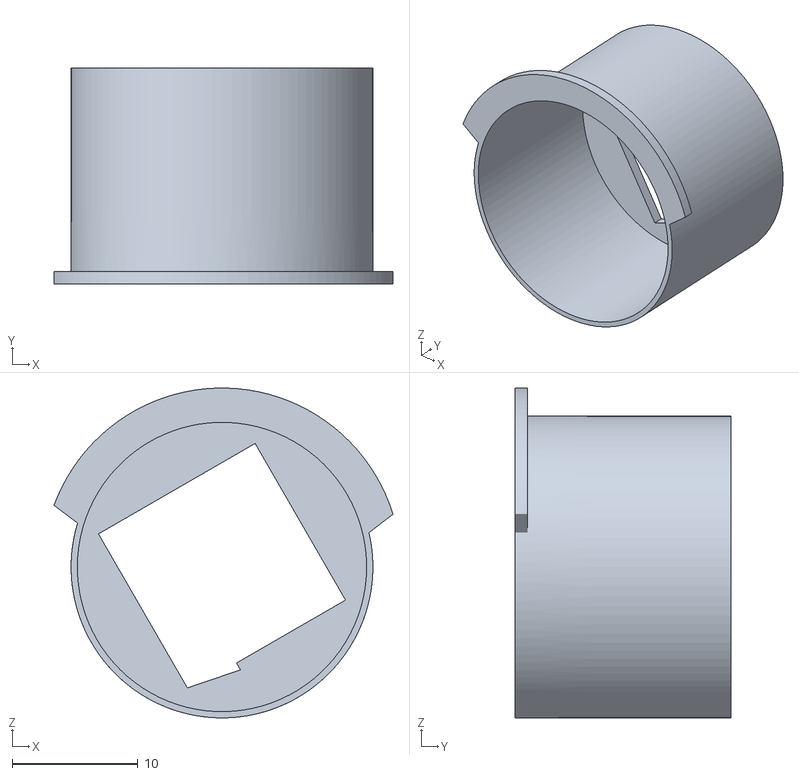
[picture p74: CAD file, 2025-12-22]
AARcontroller(v6) - Release/Body669.stl
27.0 x 17.2 x 26.2
